tebl/C64-Pi1541-III/gallery/2023-03-21 03.55.08.jpg

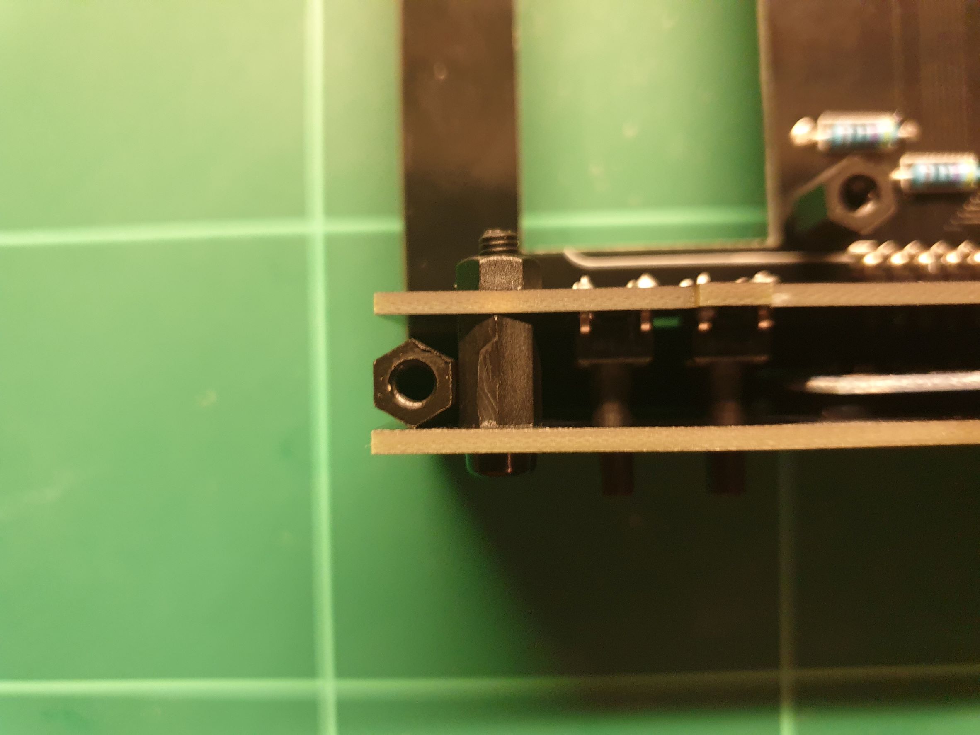
gallery/2023-03-21 03.55.08.jpg
