tebl/C64-Pi1541-III/gallery/2023-03-23 23.55.07.jpg

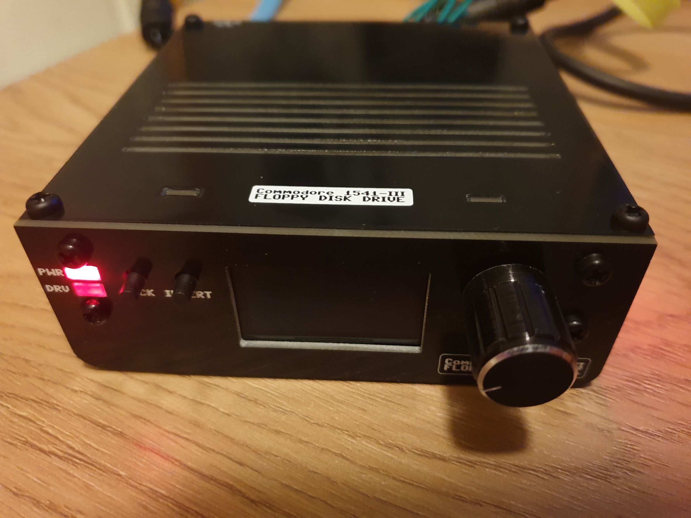
gallery/2023-03-23 23.55.07.jpg
