tebl/C64-Pi1541-III/gallery/2023-06-04 01.44.22.jpg

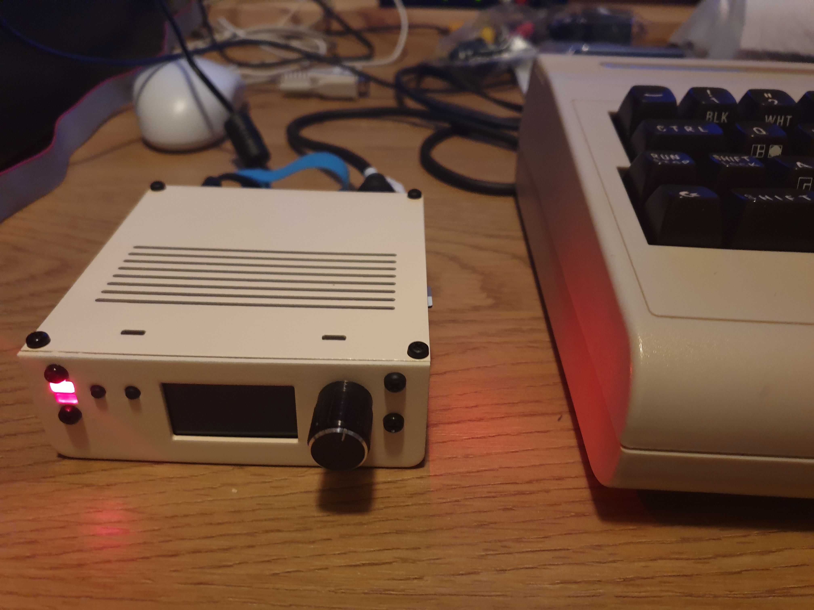
gallery/2023-06-04 01.44.22.jpg
