tebl/C64-Pi1541-III/gallery/C64 Pi1541-III Module FB1.jpg

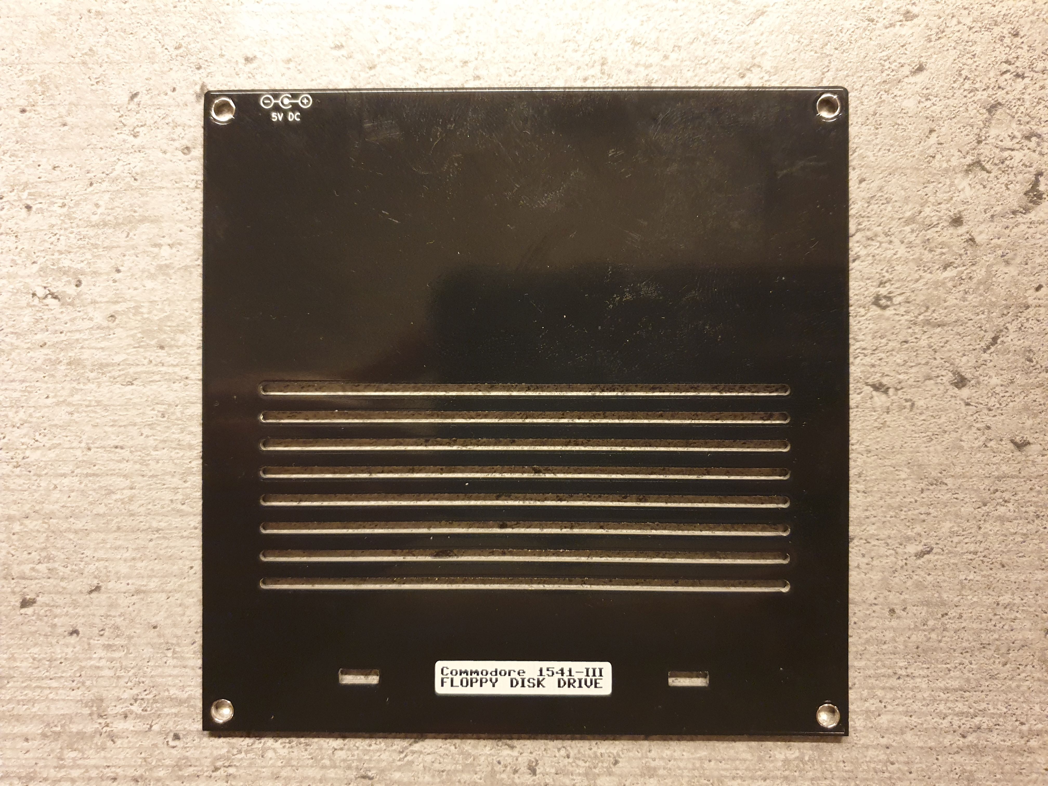
gallery/C64 Pi1541-III Module FB1.jpg
