tebl/C64-Pi1541-III/gallery/C64 Pi1541-III Module FB1.png

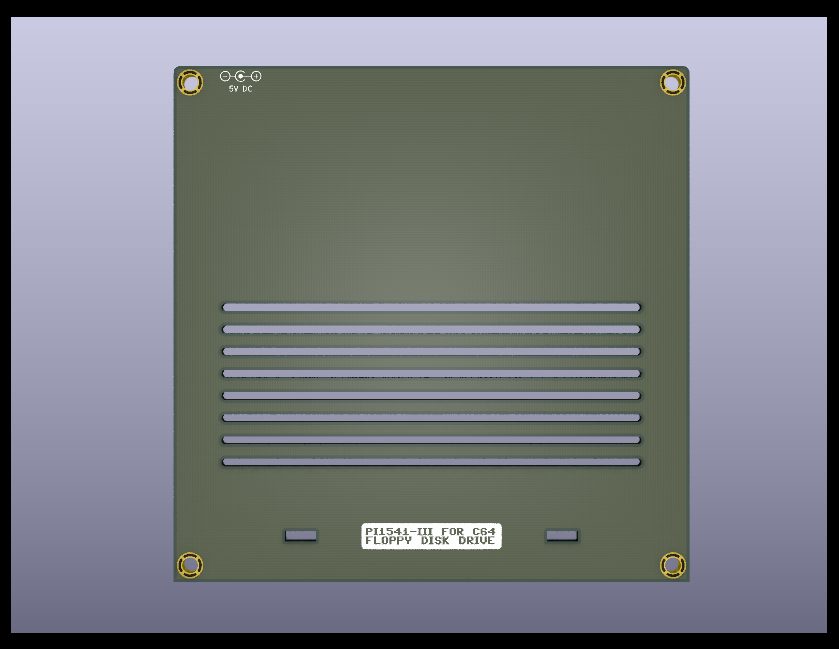
gallery/C64 Pi1541-III Module FB1.png
