tebl/C64-Pi1541-III/gallery/C64 Pi1541-III Module FB2.jpg

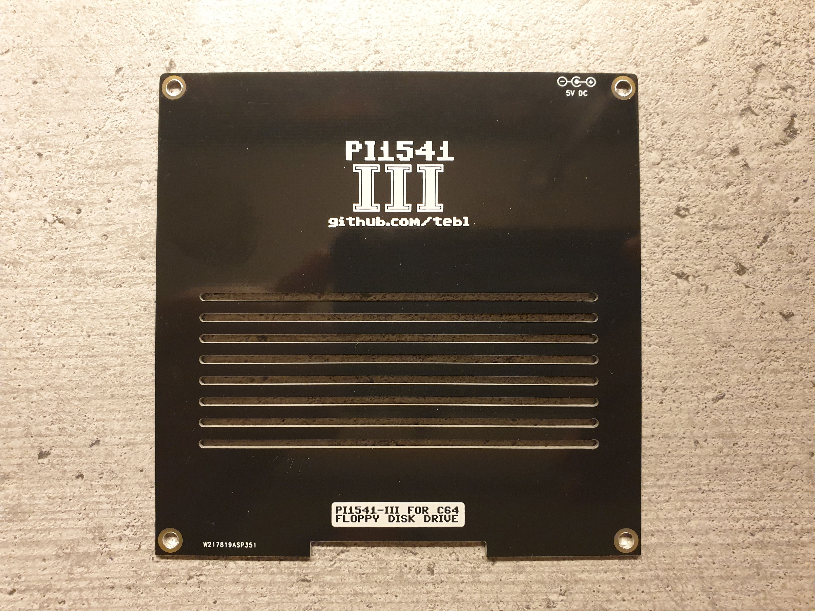
gallery/C64 Pi1541-III Module FB2.jpg
