tebl/C64-Pi1541-III/gallery/C64 Pi1541-III Module FP1.jpg

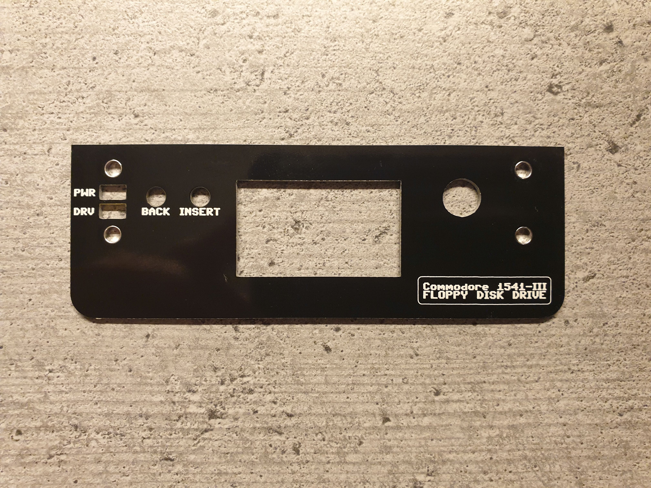
gallery/C64 Pi1541-III Module FP1.jpg
