tebl/C64-Pi1541-III/gallery/C64 Pi1541-III Module.png

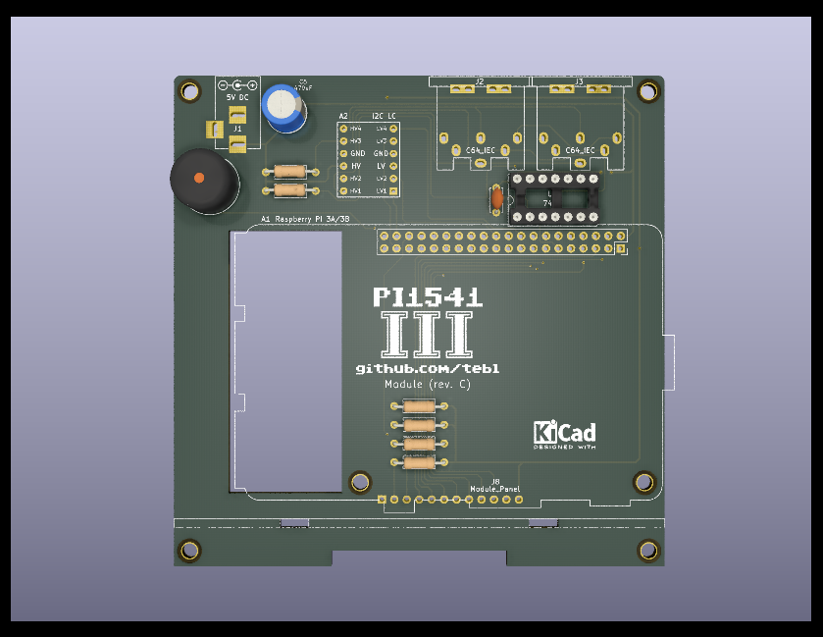
gallery/C64 Pi1541-III Module.png
