tebl/C64-Pi1541-III/gallery/build_001.jpg

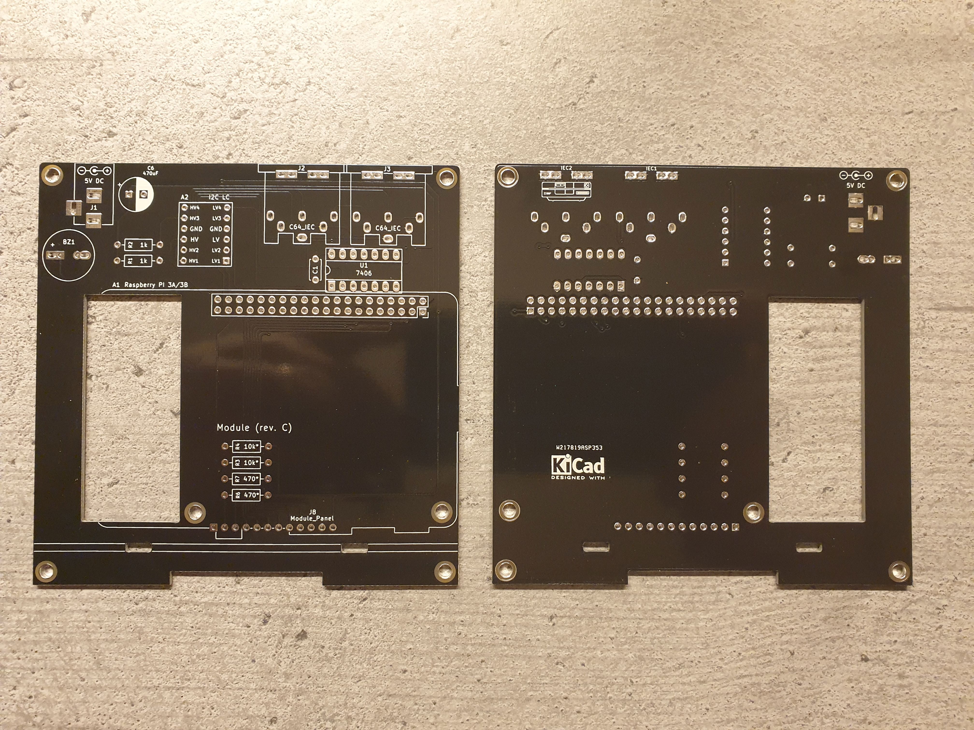
gallery/build_001.jpg
