tebl/C64-Pi1541-III/gallery/build_004.jpg

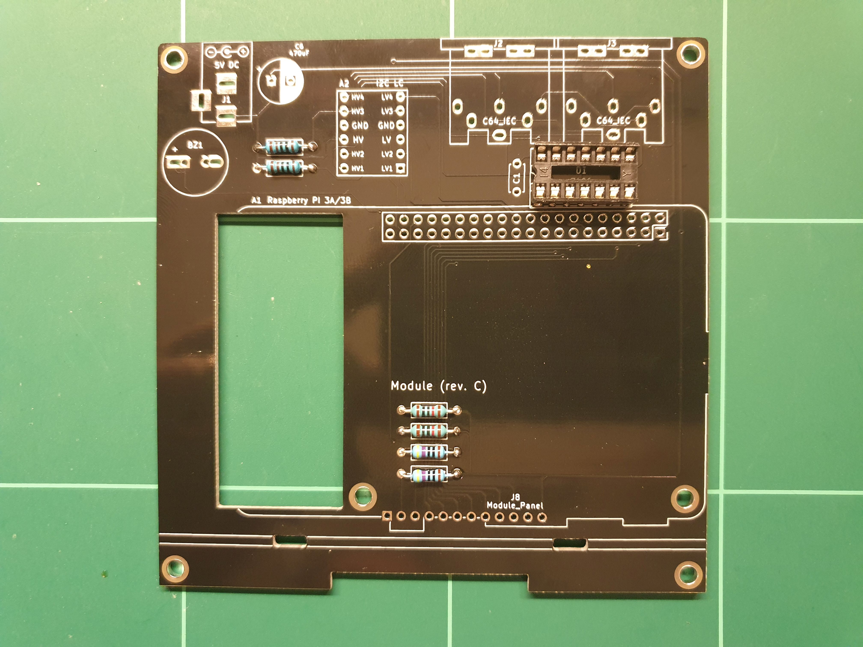
gallery/build_004.jpg
