tebl/C64-Pi1541-III/gallery/build_006A.jpg

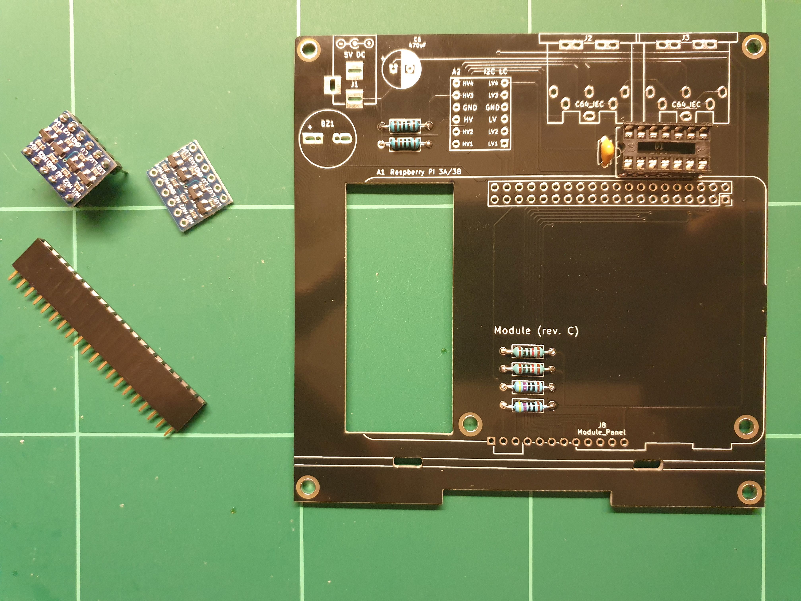
gallery/build_006A.jpg
