tebl/C64-Pi1541-III/gallery/build_007.jpg

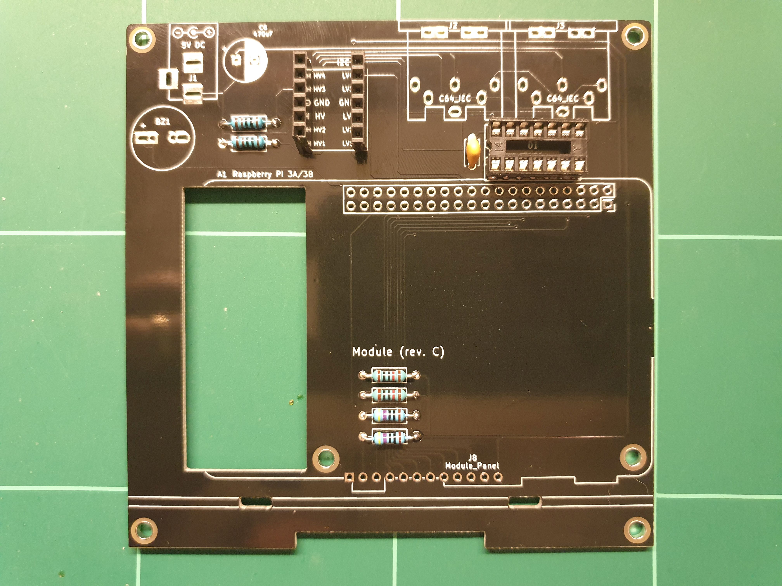
gallery/build_007.jpg
