tebl/C64-Pi1541-III/gallery/build_008.jpg

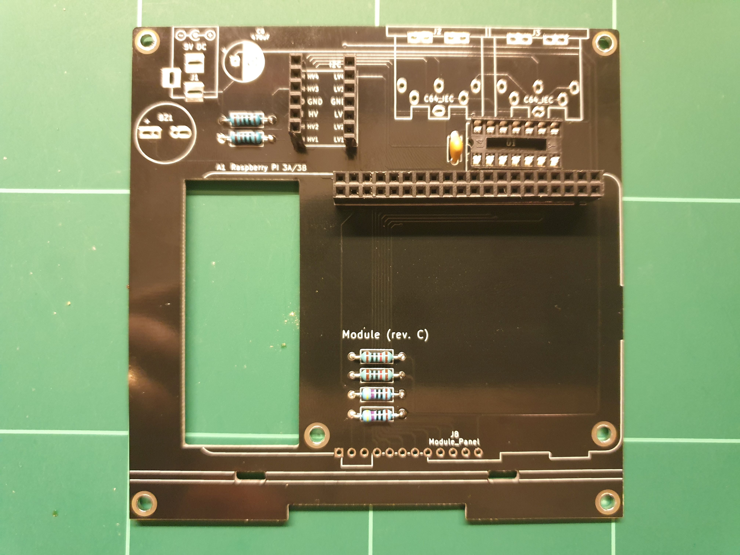
gallery/build_008.jpg
