tebl/C64-Pi1541-III/gallery/build_009.jpg

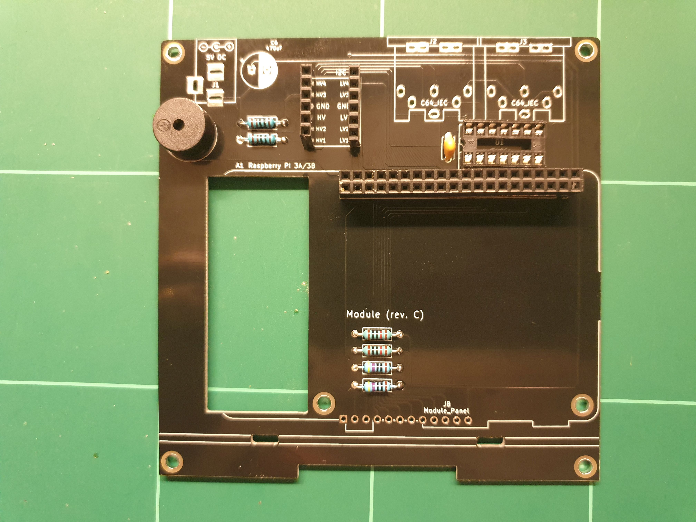
gallery/build_009.jpg
