tebl/C64-Pi1541-III/gallery/build_010.jpg

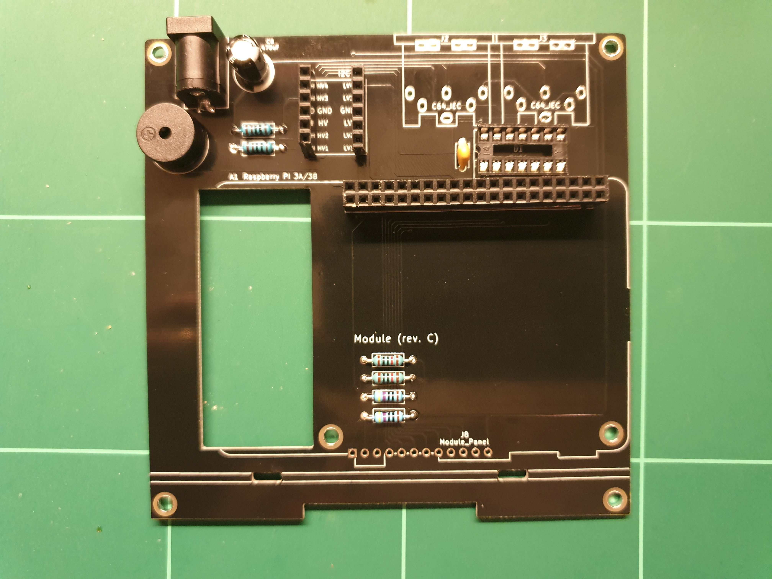
gallery/build_010.jpg
