tebl/C64-Pi1541-III/gallery/build_011.jpg

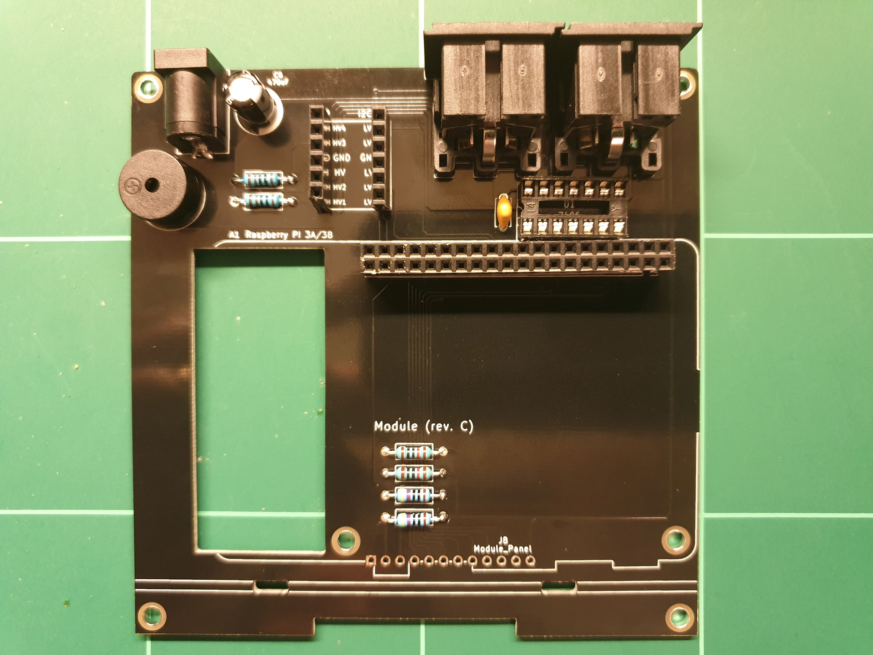
gallery/build_011.jpg
