tebl/C64-Pi1541-III/gallery/build_012.jpg

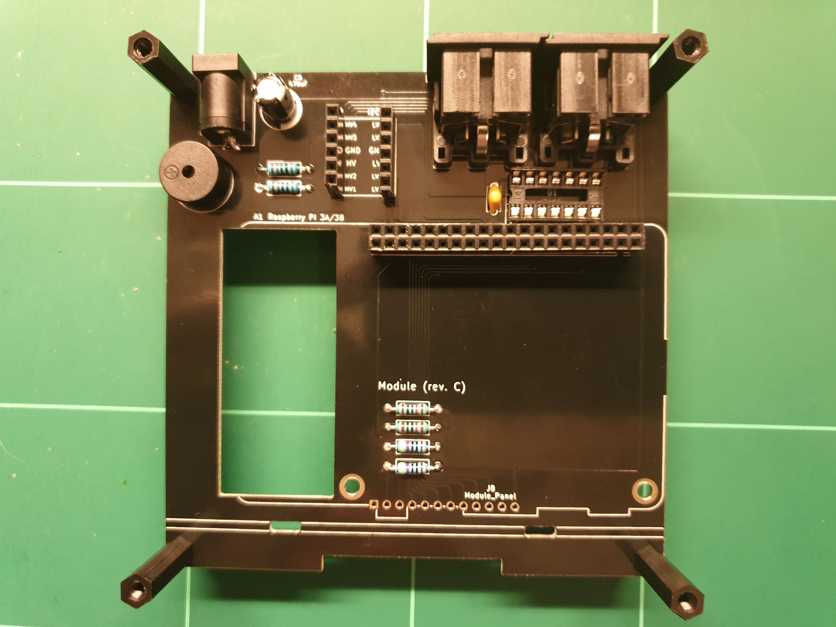
gallery/build_012.jpg
