tebl/C64-Pi1541-III/gallery/build_021A.jpg

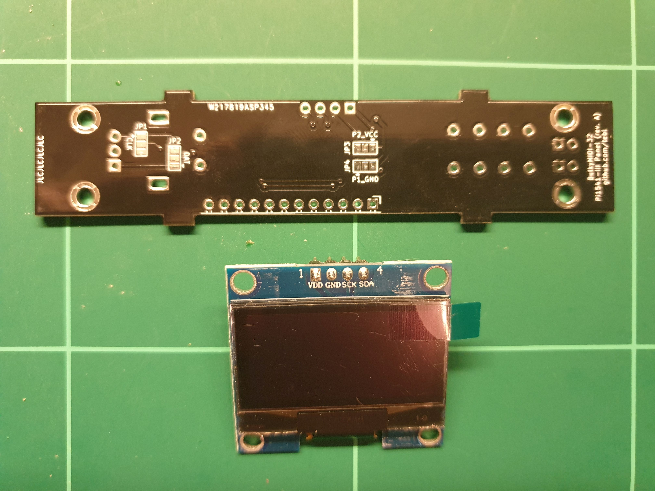
gallery/build_021A.jpg
