tebl/C64-Pi1541-III/gallery/build_021B.jpg

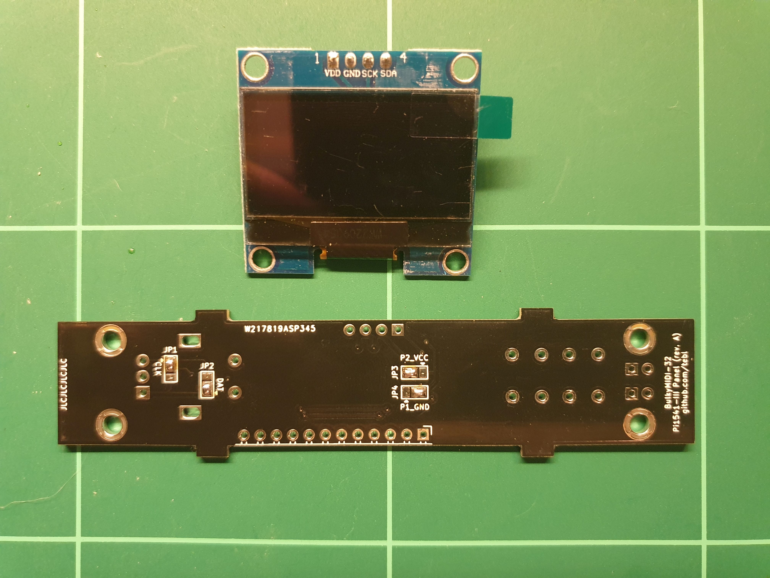
gallery/build_021B.jpg
