tebl/C64-Pi1541-III/gallery/build_022.jpg

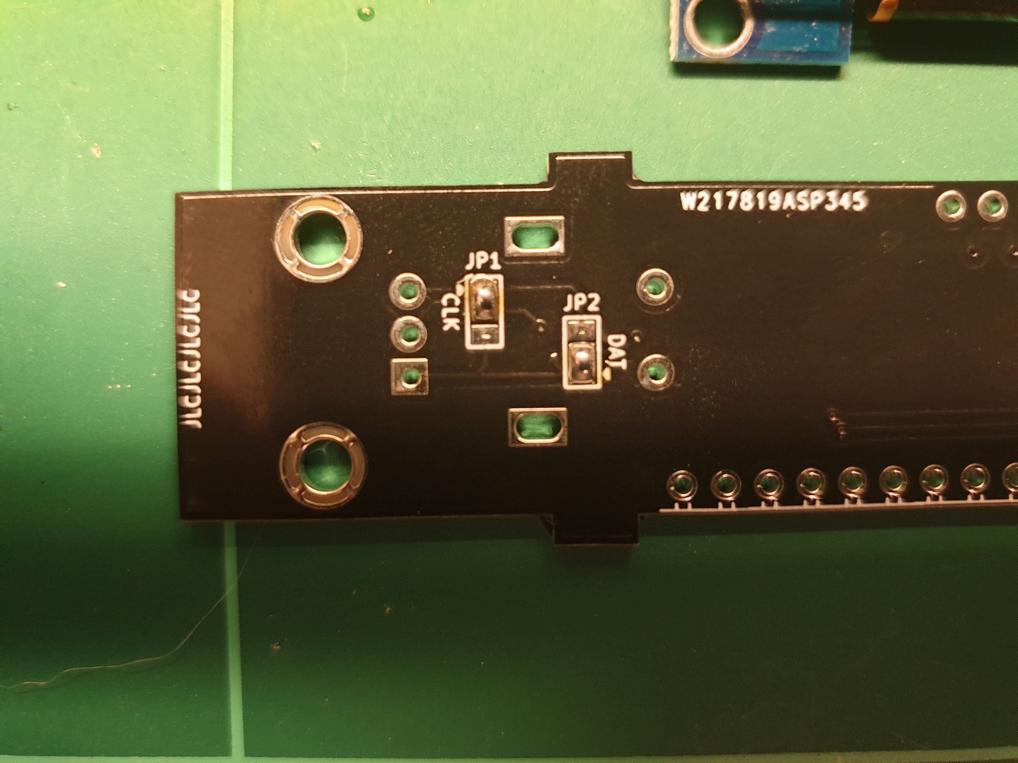
gallery/build_022.jpg
