tebl/C64-Pi1541-III/gallery/build_023.jpg

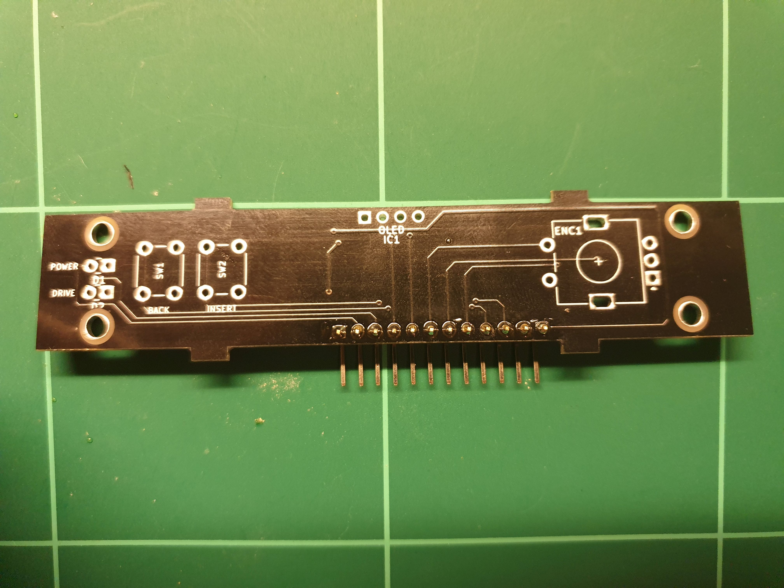
gallery/build_023.jpg
