tebl/C64-Pi1541-III/gallery/build_025.jpg

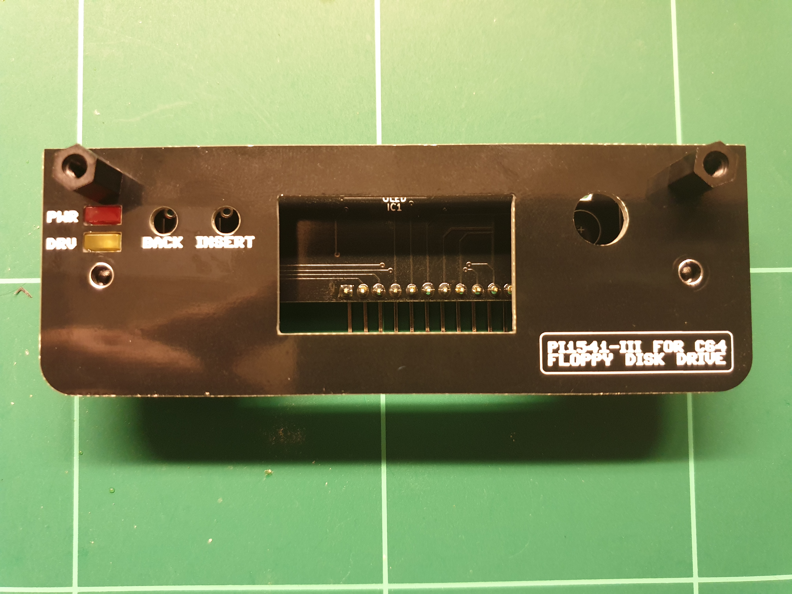
gallery/build_025.jpg
