tebl/C64-Pi1541-III/gallery/build_027.jpg

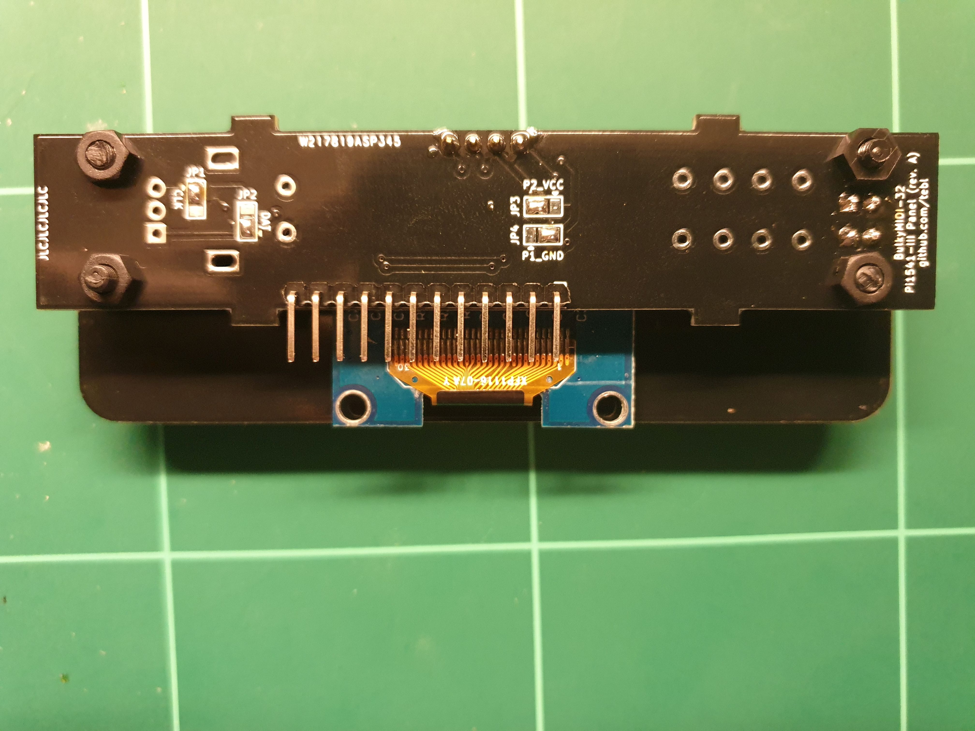
gallery/build_027.jpg
