tebl/C64-Pi1541-III/gallery/build_028.jpg

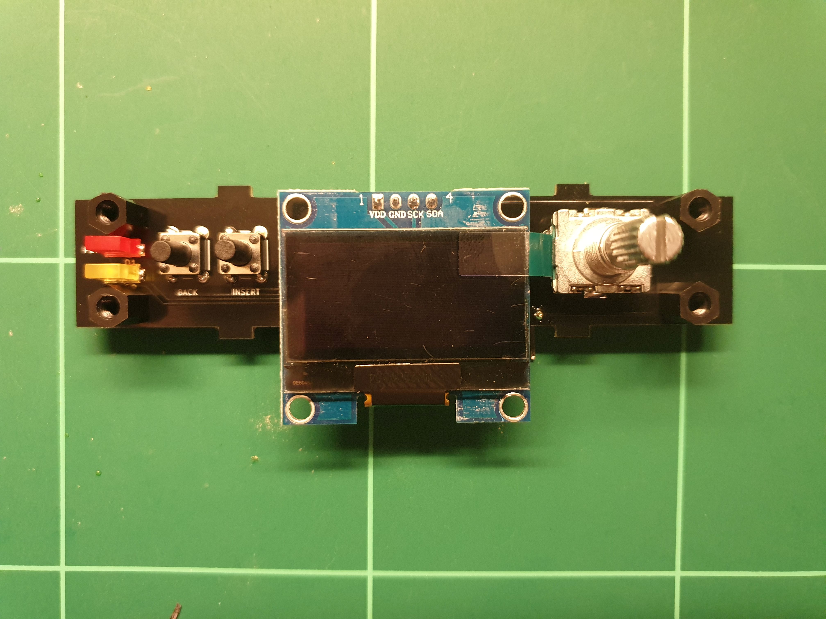
gallery/build_028.jpg
