tebl/C64-Pi1541-III/gallery/build_029.jpg

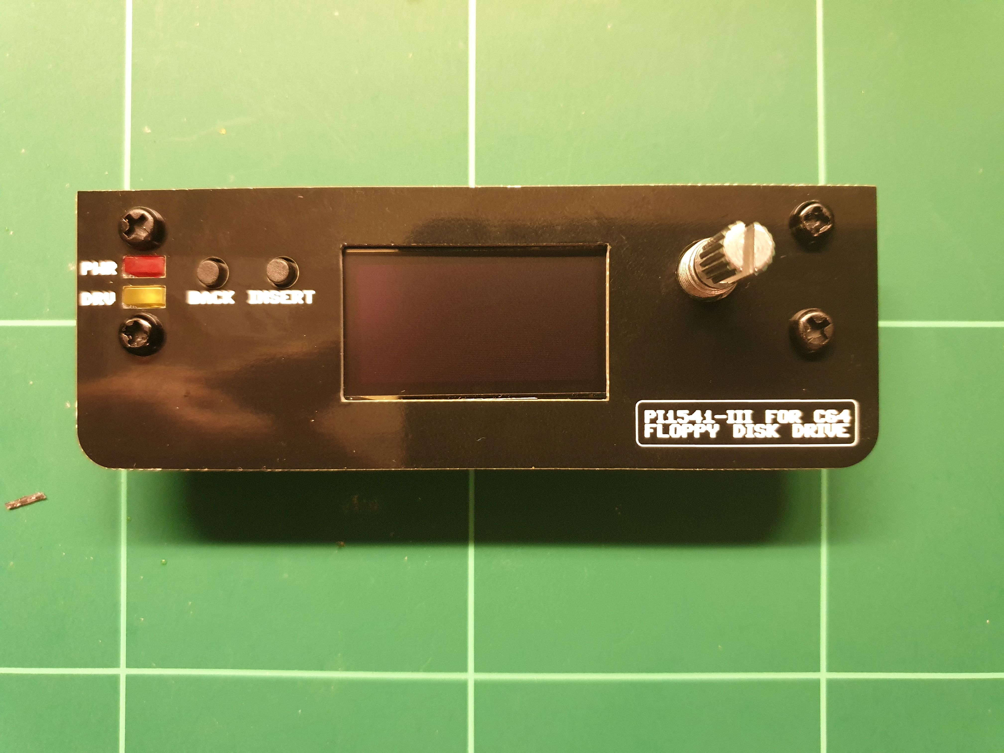
gallery/build_029.jpg
