tebl/C64-Pi1541-III/gallery/build_031.jpg

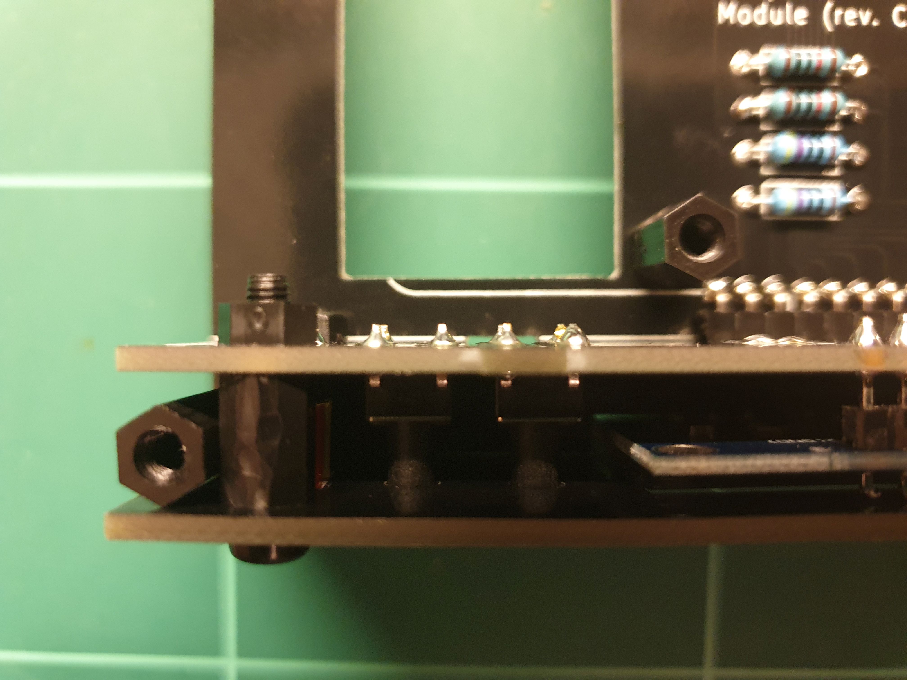
gallery/build_031.jpg
