tebl/C64-Pi1541-III/gallery/build_035.jpg

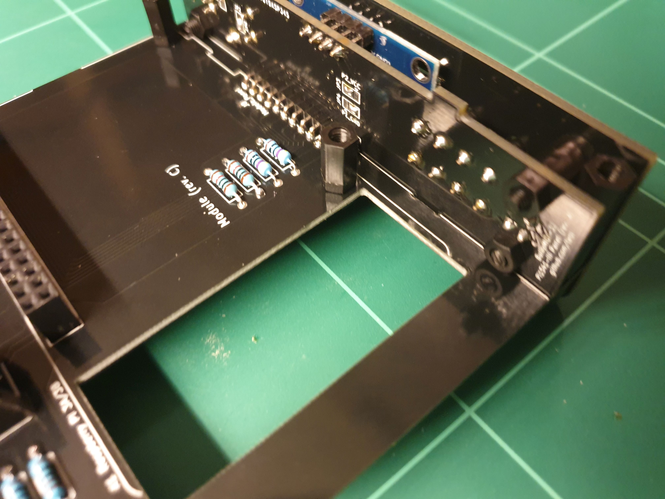
gallery/build_035.jpg
