tebl/C64-Pi1541-III/gallery/build_036.jpg

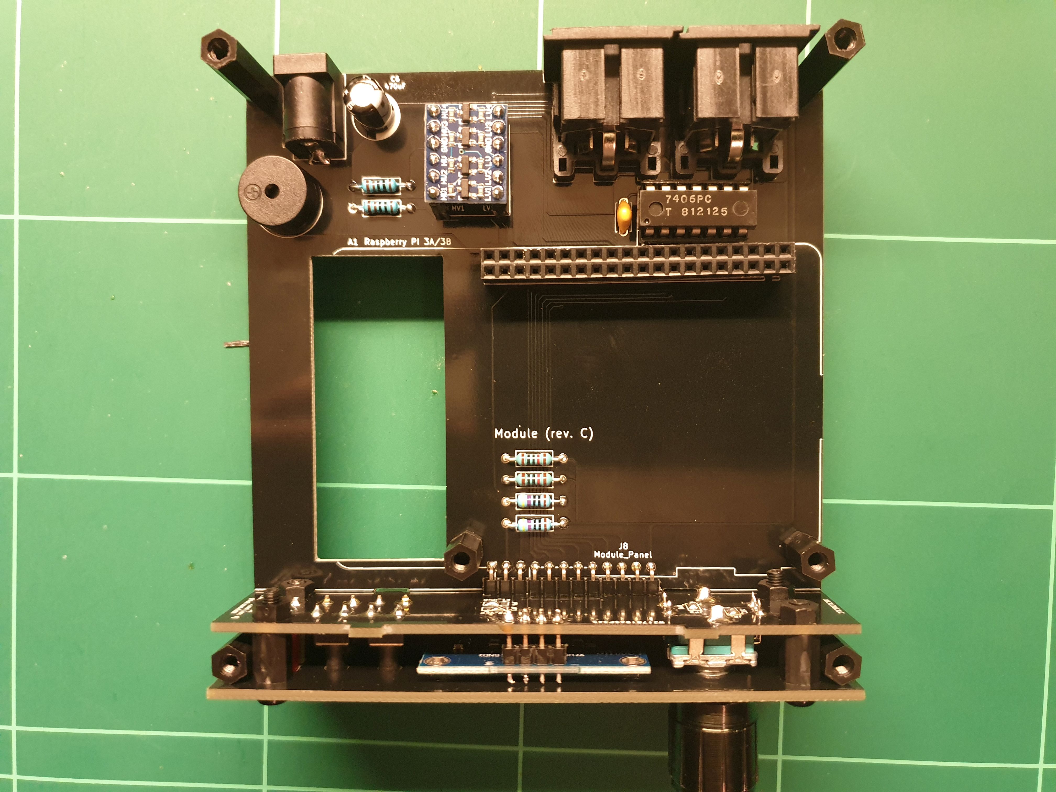
gallery/build_036.jpg
