tebl/C64-Pi1541-III/gallery/build_037.jpg

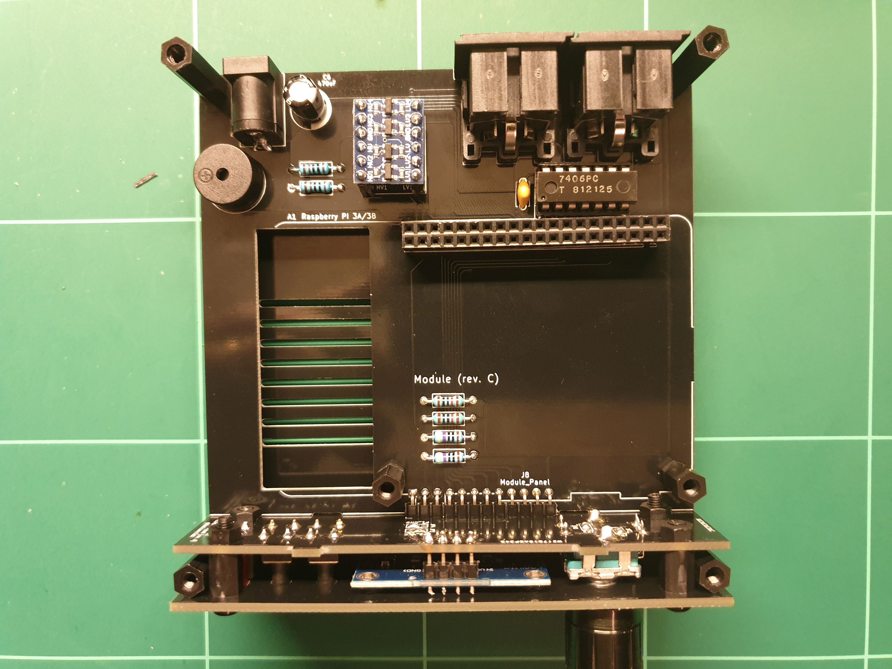
gallery/build_037.jpg
