tebl/C64-Pi1541-III/gallery/build_038.jpg

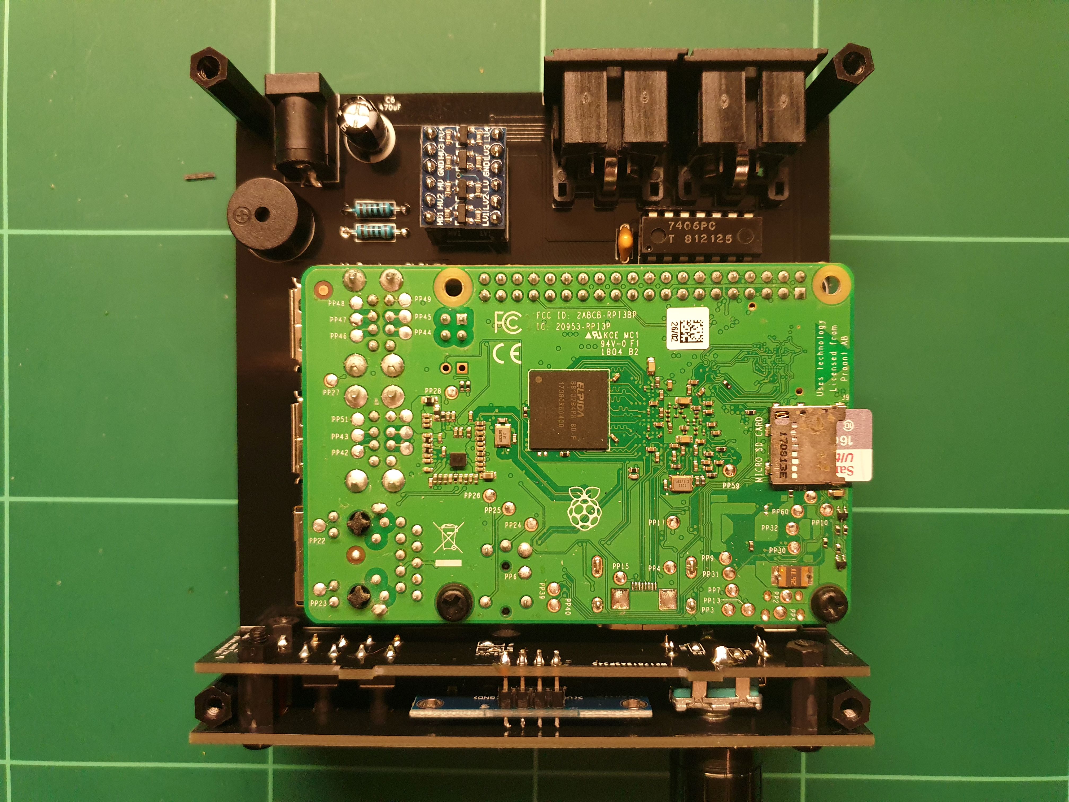
gallery/build_038.jpg
