tebl/C64-Pi1541-III/gallery/build_039.jpg

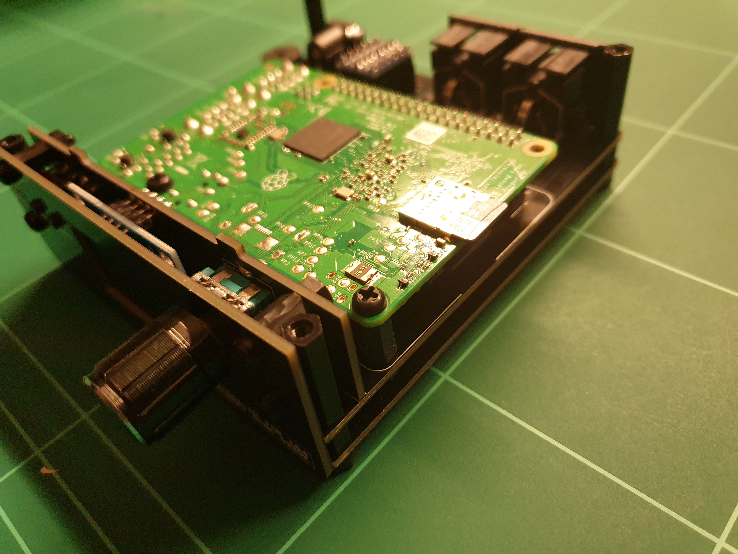
gallery/build_039.jpg
