tebl/C64-Pi1541-III/gallery/build_040.jpg

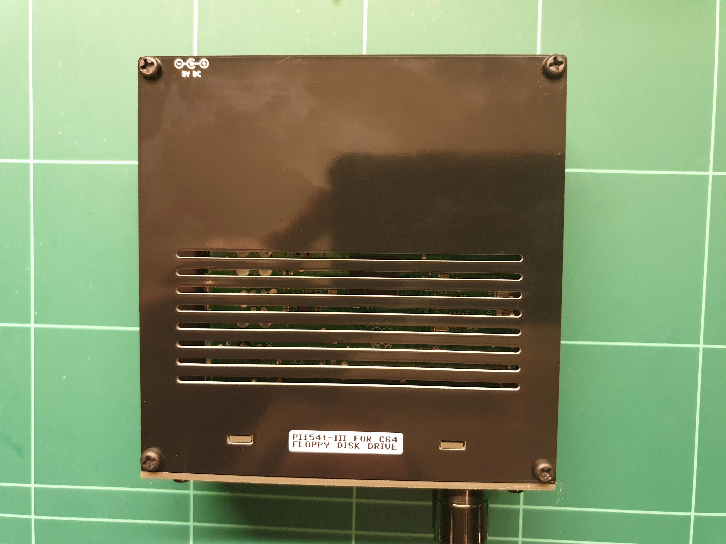
gallery/build_040.jpg
