tebl/C64-Pi1541-III/gallery/build_041.jpg

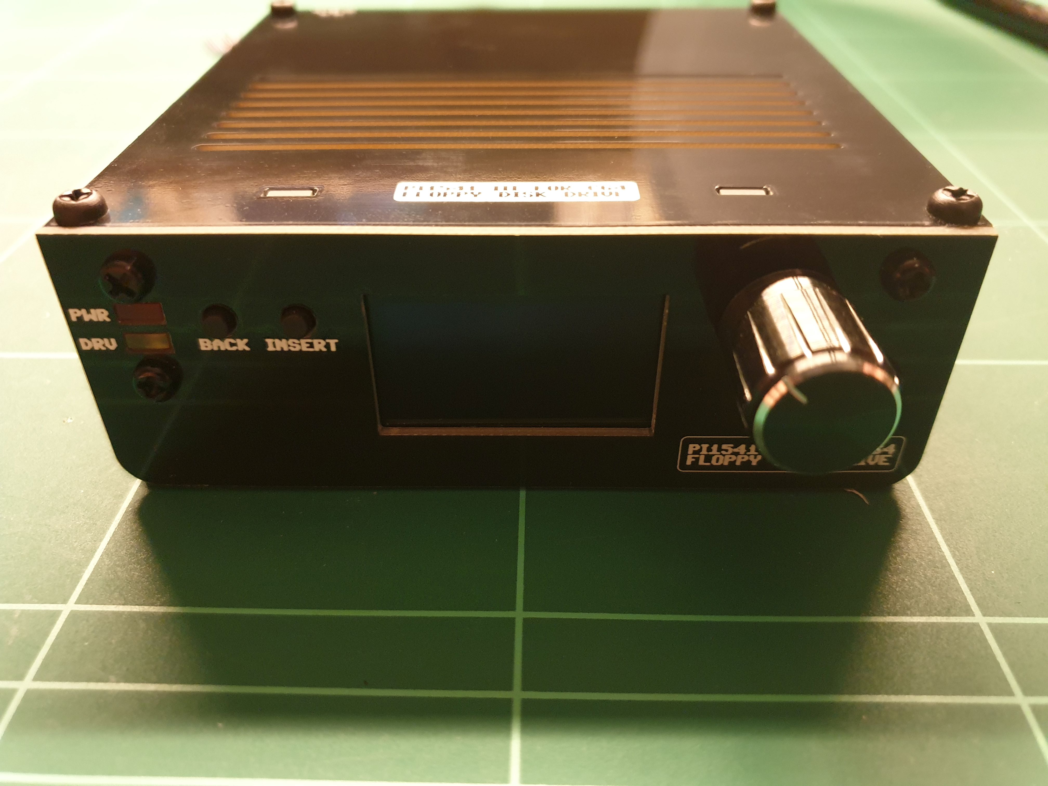
gallery/build_041.jpg
