tebl/C64-Pi1541-III/gallery/build_043.jpg

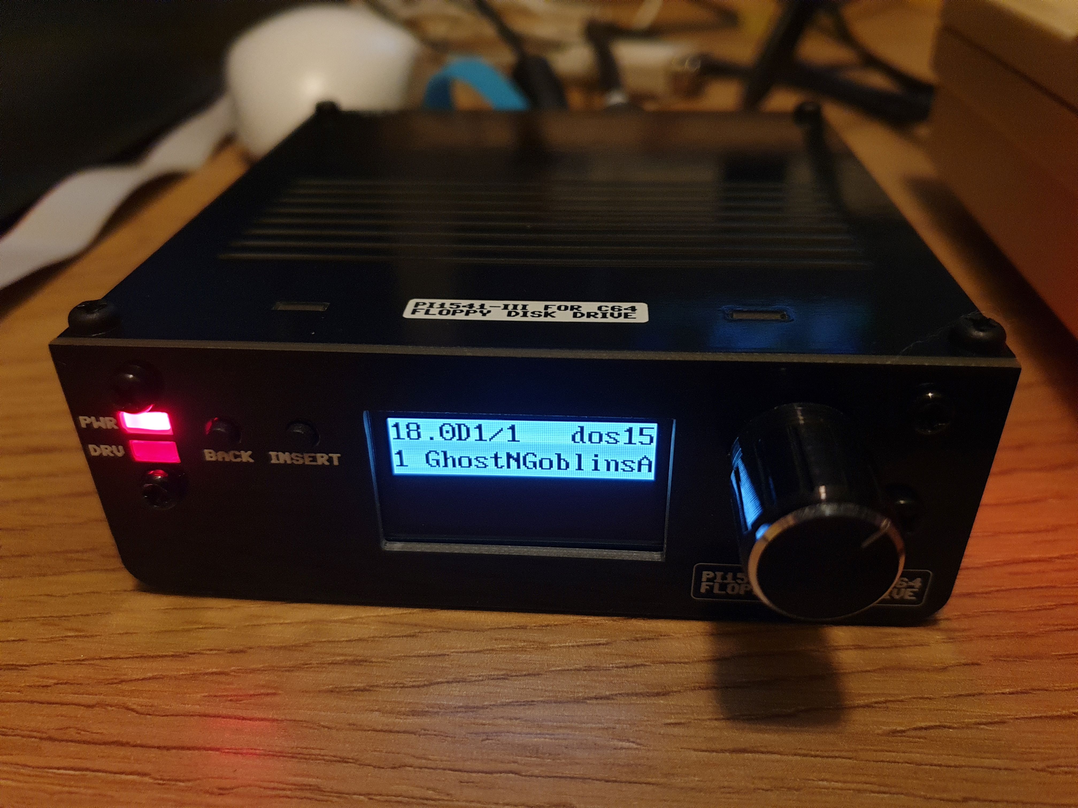
gallery/build_043.jpg
