tebl/C64-Pi1541-III/gallery/build_033.jpg

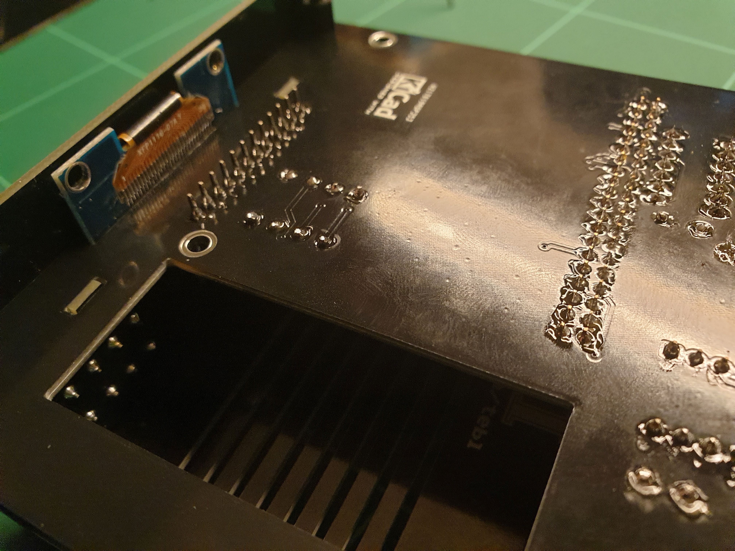
gallery/build_033.jpg
